yottanami/yottasynth/src/app_state.cpp

#include "app_state.h"

namespace {
constexpr SequenceStep kDefaultSequence[16] = {
    {true, false, 60, 78},  {true, false, 62, 72},  {true, false, 67, 82},
    {false, false, 67, 70}, {true, false, 60, 78},  {true, false, 64, 72},
    {true, false, 69, 82},  {false, false, 69, 70}, {true, false, 60, 78},
    {true, false, 62, 72},  {true, false, 67, 82},  {false, false, 67, 70},
    {true, false, 72, 78},  {true, false, 69, 72},  {true, false, 64, 82},
    {false, false, 60, 70},
};
}

AppState::AppState() {
  for (uint8_t index = 0; index < 16; ++index) {
    sequencer.steps[index] = kDefaultSequence[index];
  }
}

AppState &AppState::instance() {
  static AppState state;
  return state;
}

namespace {
float clampUnit(float value) {
  if (value < 0.0f) {
    return 0.0f;
  }
  if (value > 1.0f) {
    return 1.0f;
  }
  return value;
}
}

void AppState::setPage(PageId page) {
  ui.page = page;
  ui.show_input_test = false;
  ui.confirm_clear_sequence = false;
  ui.dirty = true;
}

void AppState::setInputTestVisible(bool visible) {
  ui.show_input_test = visible;
  ui.confirm_clear_sequence = false;
  ui.dirty = true;
}

void AppState::markDirty() {
  ui.dirty = true;
}

Mode AppState::currentMode() const {
  if (ui.show_input_test) {
    return Mode::INPUT_TEST;
  }

  switch (ui.page) {
    case PageId::ARP:
      return Mode::ARPEGGIATOR;
    case PageId::SEQ:
      return Mode::SEQUENCER;
    case PageId::SETTINGS:
    case PageId::PLAY:
    case PageId::OSC_MIX:
    case PageId::FILTER_AMP:
    case PageId::MOD:
    case PageId::FX:
    default:
      return Mode::SYNTHESIZER;
  }
}

void AppState::updateMidiDevice(bool connected, uint16_t vendor_id, uint16_t product_id) {
  if (midi.connected == connected && midi.vendor_id == vendor_id &&
      midi.product_id == product_id) {
    return;
  }

  midi.connected = connected;
  midi.vendor_id = vendor_id;
  midi.product_id = product_id;
  ui.dirty = true;
}

void AppState::registerMidiNote(uint8_t note, uint8_t velocity) {
  midi.last_note = note;
  midi.last_velocity = velocity;
  midi.last_note_ms = millis();
  midi.note_recent = true;
  ui.dirty = true;
}

void AppState::refreshTransientStatus(unsigned long now_ms) {
  const bool recent = midi.connected && (now_ms - midi.last_note_ms) < 1500UL;
  if (midi.note_recent != recent) {
    midi.note_recent = recent;
    ui.dirty = true;
  }
}

void AppState::updateAudioStatus(bool codec_ready, bool self_test_active) {
  if (audio.codec_ready == codec_ready && audio.self_test_active == self_test_active) {
    return;
  }

  audio.codec_ready = codec_ready;
  audio.self_test_active = self_test_active;
  ui.dirty = true;
}

void AppState::setOutputVolume(float volume) {
  const float clamped = clampUnit(volume);
  if (audio.output_volume == clamped) {
    return;
  }

  audio.output_volume = clamped;
  ui.dirty = true;
}

const char *pageTitle(PageId page) {
  switch (page) {
    case PageId::PLAY:
      return "PLAY";
    case PageId::OSC_MIX:
      return "OSC / MIX";
    case PageId::FILTER_AMP:
      return "FILTER / AMP";
    case PageId::MOD:
      return "MOD";
    case PageId::FX:
      return "FX";
    case PageId::ARP:
      return "ARPEGGIATOR";
    case PageId::SEQ:
      return "SEQUENCER";
    case PageId::SETTINGS:
      return "SETTINGS";
    default:
      return "PLAY";
  }
}

const char *fxModeLabel(FxMode mode) {
  switch (mode) {
    case FxMode::ECHO:
      return "ECHO";
    case FxMode::REVERB:
      return "REVERB";
    case FxMode::DRIVE:
      return "DRIVE";
    default:
      return "ECHO";
  }
}

const char *clockSourceLabel(ClockSource source) {
  switch (source) {
    case ClockSource::INTERNAL:
      return "INT";
    case ClockSource::EXTERNAL:
      return "EXT";
    default:
      return "INT";
  }
}

const char *arpModeLabel(ArpMode mode) {
  switch (mode) {
    case ArpMode::UP:
      return "UP";
    case ArpMode::DOWN:
      return "DOWN";
    case ArpMode::UP_DOWN:
      return "UP/DOWN";
    case ArpMode::RANDOM:
      return "RANDOM";
    default:
      return "UP";
  }
}

const char *lfoTargetLabel(LfoTarget target) {
  switch (target) {
    case LfoTarget::OFF:
      return "OFF";
    case LfoTarget::FILTER:
      return "FILTER";
    case LfoTarget::PITCH:
      return "PITCH";
    default:
      return "OFF";
  }
}

const char *oscWaveLabel(OscWave wave) {
  switch (wave) {
    case OscWave::SAW:
      return "SAW";
    case OscWave::SINE:
      return "SINE";
    case OscWave::SQUARE:
      return "SQR";
    case OscWave::TRIANGLE:
      return "TRI";
    default:
      return "SAW";
  }
}

const char *tuningLabel(TuningId tuning) {
  switch (tuning) {
    case TuningId::STANDARD:
      return "Standard";
    case TuningId::SHUR:
      return "Shur";
    case TuningId::ABUATA:
      return "Abuata";
    case TuningId::DASHTI:
      return "Dashti";
    case TuningId::BAYAT_E_TORK:
      return "Bayat-e Tork";
    case TuningId::AFSHARI:
      return "Afshari";
    case TuningId::SEGAH:
      return "Segah";
    case TuningId::CHAHARGAH:
      return "Chahargah";
    case TuningId::HOMAYUN:
      return "Homayun";
    case TuningId::BAYAT_E_ESFAHAN:
      return "Bayat-e Esfahan";
    case TuningId::NAVA:
      return "Nava";
    case TuningId::MAHUR:
      return "Mahur";
    case TuningId::RAST_PANJGAH:
      return "Rast-Panjgah";
    default:
      return "Standard";
  }
}

uint8_t tuningCount() {
  return static_cast<uint8_t>(TuningId::RAST_PANJGAH) + 1U;
}
